ifilot/pico-sst39sf0x0-programmer/gui/tests/tst_mainwindow.cpp

#include <QtTest/QtTest>

#include "mainwindow.h"
#include "colorcontrast.h"
#include "support/emulated_serial_transport.h"
#include "support/fault_injecting_transport.h"

#include <QComboBox>
#include <QFile>
#include <QGroupBox>
#include <QLabel>
#include <QMessageBox>
#include <QProgressBar>
#include <QPushButton>
#include <QRegularExpression>
#include <QScrollArea>
#include <QScrollBar>
#include <QSet>
#include <QTimer>

#include <memory>

namespace {

class ModalDialogWatcher : public QObject {
public:
    QStringList messages;

    ModalDialogWatcher() {
        this->timer.setInterval(10);
        connect(&this->timer, &QTimer::timeout, this, &ModalDialogWatcher::captureAndAcceptDialogs);
        this->timer.start();
    }

    ~ModalDialogWatcher() override {
        this->timer.stop();
    }

private:
    QTimer timer;
    QSet<QWidget*> handled;

private:
    void captureAndAcceptDialogs() {
        const auto widgets = QApplication::topLevelWidgets();
        for(QWidget* widget : widgets) {
            if(this->handled.contains(widget)) {
                continue;
            }

            if(auto* box = qobject_cast<QMessageBox*>(widget)) {
                this->messages.append(box->text());
                this->handled.insert(widget);
                QTimer::singleShot(0, box, &QMessageBox::accept);
            }
        }
    }
};

}

class MainWindowTest : public QObject {
    Q_OBJECT

private:
    static MainWindow::SerialInterfaceFactory buildFactory(const std::shared_ptr<FirmwareEmulatorBackend>& backend) {
        return [backend](const std::string& portname) {
            return std::make_shared<SerialInterface>(portname, [backend](const std::string&) {
                return backend->create_transport();
            });
        };
    }

    static MainWindow::SerialInterfaceFactory buildFaultFactory(const std::shared_ptr<FirmwareEmulatorBackend>& backend,
                                                                const std::string& targetCommand,
                                                                FaultInjectingTransport::FaultMode mode) {
        return [backend, targetCommand, mode](const std::string& portname) {
            return std::make_shared<SerialInterface>(portname, [backend, targetCommand, mode](const std::string&) {
                return std::make_unique<FaultInjectingTransport>(
                    backend->create_transport(),
                    targetCommand,
                    mode
                );
            });
        };
    }

    static QComboBox* serialPortCombo(MainWindow& window) {
        return window.findChild<QComboBox*>("comboboxSerialPorts");
    }

    static QLabel* boardIdLabel(MainWindow& window) {
        return window.findChild<QLabel*>("labelBoardId");
    }

    static QLabel* serialLabel(MainWindow& window) {
        return window.findChild<QLabel*>("labelSerial");
    }

    static QLabel* chipTypeLabel(MainWindow& window) {
        return window.findChild<QLabel*>("labelChipType");
    }

    static QPushButton* button(MainWindow& window, const char* objectName) {
        return window.findChild<QPushButton*>(objectName);
    }

    static QProgressBar* progressBar(MainWindow& window) {
        return window.findChild<QProgressBar*>("progressBarLoad");
    }

    static HexViewWidget* hexView(MainWindow& window) {
        return window.findChild<HexViewWidget*>("hexViewWidget");
    }

    static void addEmulatedPort(MainWindow& window, const QString& portName = "emu") {
        auto* combo = serialPortCombo(window);
        QVERIFY(combo != nullptr);
        combo->addItem(portName);
        combo->setCurrentText(portName);
    }

private slots:
    void select_com_port_updates_labels_and_enables_buttons();
    void read_chip_id_updates_ui_state();
    void read_rom_populates_hex_view();
    void flash_rom_quick_runs_program_and_verify_workflow();
    void flash_rom_quick_worker_abort_is_reported();
    void destruction_waits_for_active_read();
    void menu_actions_have_visible_icons();
    void right_control_panel_fits_scroll_viewport();
    void hex_viewer_color_presets_and_swatches_are_accessible();
};

void MainWindowTest::hex_viewer_color_presets_and_swatches_are_accessible() {
    QCOMPARE(contrastingTextColor(QColor(Qt::white)), QColor(Qt::black));
    QCOMPARE(contrastingTextColor(QColor(Qt::black)), QColor(Qt::white));
    QCOMPARE(contrastingTextColor(QColor(QStringLiteral("#fdf6e3"))), QColor(Qt::black));
    QCOMPARE(contrastingTextColor(QColor(QStringLiteral("#282a36"))), QColor(Qt::white));

    SettingsWidget widget;
    auto* themes = widget.findChild<QComboBox*>("hexViewerThemeComboBox");
    QVERIFY(themes != nullptr);
    const QStringList accessibleThemes = {
        QStringLiteral("Dracula"),
        QStringLiteral("Dracula Alucard (Light)"),
        QStringLiteral("Nord"),
        QStringLiteral("Gruvbox Dark"),
        QStringLiteral("Catppuccin Mocha")
    };
    for(const QString& themeName : accessibleThemes) {
        const int index = themes->findText(themeName);
        QVERIFY2(index >= 0, qPrintable(themeName));
        const QVariantList colors = themes->itemData(index).toList();
        QCOMPARE(colors.size(), 6);
        const QColor background(colors.constFirst().toUInt());
        for(int i = 1; i < colors.size(); ++i) {
            const QColor foreground(colors.at(i).toUInt());
            QVERIFY2(colorContrastRatio(background, foreground) >= 4.5,
                     qPrintable(themeName + QStringLiteral(" color ") + foreground.name()));
        }
    }

    const int saa5050Index = themes->findText(QStringLiteral("SAA5050"));
    QVERIFY(saa5050Index >= 0);
    const QVariantList saa5050 = themes->itemData(saa5050Index).toList();
    QCOMPARE(saa5050.size(), 6);
    QCOMPARE(saa5050.at(3).toUInt(), 0xFFFFFFFFu);

    const auto swatches = widget.findChildren<QPushButton*>(
        QRegularExpression(QStringLiteral("^colorSwatch_")));
    QCOMPARE(swatches.size(), 6);
    for(QPushButton* swatch : swatches) {
        const QColor color = swatch->property("swatchColor").value<QColor>();
        QVERIFY(color.isValid());
        QCOMPARE(swatch->text(), color.name(QColor::HexRgb));
        QVERIFY(swatch->styleSheet().contains(contrastingTextColor(color).name()));
    }
}

void MainWindowTest::right_control_panel_fits_scroll_viewport() {
    auto logs = std::make_shared<QStringList>();
    MainWindow window(logs);
    window.resize(1000, 800);
    window.show();
    QApplication::processEvents();

    auto* scrollArea = window.findChild<QScrollArea*>("rightControlScrollArea");
    auto* controls = window.findChild<QWidget*>("rightControlContainer");
    QVERIFY(scrollArea != nullptr);
    QVERIFY(controls != nullptr);
    QCOMPARE(scrollArea->horizontalScrollBar()->maximum(), 0);
    QCOMPARE(controls->width(), scrollArea->viewport()->width());

    const QStringList groupNames = {
        QStringLiteral("serialInterfaceGroup"),
        QStringLiteral("romImagesGroup"),
        QStringLiteral("operationsGroup")
    };
    for(const QString& name : groupNames) {
        auto* group = controls->findChild<QGroupBox*>(name);
        QVERIFY2(group != nullptr, qPrintable(name));
        QVERIFY2(group->geometry().right() < controls->width(), qPrintable(name));
    }
}

void MainWindowTest::menu_actions_have_visible_icons() {
    auto logs = std::make_shared<QStringList>();
    MainWindow window(logs);

    const auto menuBarActions = window.menuBar()->actions();
    QCOMPARE(menuBarActions.size(), 3);
    for(QAction* menuBarAction : menuBarActions) {
        QMenu* menu = menuBarAction->menu();
        QVERIFY(menu != nullptr);
        for(QAction* action : menu->actions()) {
            QVERIFY2(!action->icon().isNull(), qPrintable(action->text()));
            QVERIFY2(action->isIconVisibleInMenu(), qPrintable(action->text()));
        }
    }

    QPushButton* romButton = nullptr;
    for(QPushButton* candidate : window.findChildren<QPushButton*>()) {
        if(candidate->text() == QStringLiteral("Select other ROM")) {
            romButton = candidate;
            break;
        }
    }

    QVERIFY(romButton != nullptr);
    QVERIFY(romButton->menu() != nullptr);
    QCOMPARE(romButton->menu()->actions().size(), 2);

    for(QAction* action : romButton->menu()->actions()) {
        QVERIFY2(!action->icon().isNull(), qPrintable(action->text()));
        QVERIFY2(action->isIconVisibleInMenu(), qPrintable(action->text()));
        QVERIFY2(action->menu() != nullptr, qPrintable(action->text()));
    }

    QMenu* p2000tMenu = romButton->menu()->actions().at(0)->menu();
    QMenu* p2000mMenu = romButton->menu()->actions().at(1)->menu();
    QCOMPARE(p2000tMenu->title(), QStringLiteral("Philips P2000T"));
    QCOMPARE(p2000mMenu->title(), QStringLiteral("Philips P2000M"));
    QCOMPARE(p2000tMenu->actions().size(), 14);
    QCOMPARE(p2000mMenu->actions().size(), 2);
    QVERIFY(p2000tMenu->menuAction()->icon().cacheKey()
            != p2000tMenu->actions().constFirst()->icon().cacheKey());
    QVERIFY(p2000mMenu->menuAction()->icon().cacheKey()
            != p2000mMenu->actions().constFirst()->icon().cacheKey());

    for(QAction* action : p2000tMenu->actions()) {
        QVERIFY2(!action->icon().isNull(), qPrintable(action->text()));
        QVERIFY2(action->isIconVisibleInMenu(), qPrintable(action->text()));
        QVERIFY2(action->property("image_name").isValid(), qPrintable(action->text()));
    }

    QCOMPARE(p2000mMenu->actions().at(0)->text(), QStringLiteral("MCPM"));
    QCOMPARE(p2000mMenu->actions().at(1)->text(), QStringLiteral("UCSD Pascal"));
    for(QAction* action : p2000mMenu->actions()) {
        QVERIFY2(!action->icon().isNull(), qPrintable(action->text()));
        QVERIFY2(action->isIconVisibleInMenu(), qPrintable(action->text()));

        QFile file(QStringLiteral(":/assets/roms/") + action->property("image_name").toString());
        QVERIFY2(file.open(QIODevice::ReadOnly), qPrintable(file.fileName()));
        QCOMPARE(file.size(), qint64(16 * 1024));

        const QByteArray data = file.readAll();
        if(action->text() == QStringLiteral("MCPM")) {
            QCOMPARE(data.right(8 * 1024), QByteArray(8 * 1024, static_cast<char>(0xFF)));
        }
    }
}

void MainWindowTest::select_com_port_updates_labels_and_enables_buttons() {
    auto backend = std::make_shared<FirmwareEmulatorBackend>();
    auto logs = std::make_shared<QStringList>();
    MainWindow window(logs, nullptr, buildFactory(backend));

    addEmulatedPort(window);

    QVERIFY(QMetaObject::invokeMethod(&window, "select_com_port", Qt::DirectConnection));

    QCOMPARE(serialLabel(window)->text(), QString("Port: emu"));
    QVERIFY(boardIdLabel(window)->text().contains("PICOSST39-V1.3.0"));
    QVERIFY(button(window, "buttonIdentifyChip")->isEnabled());
    QVERIFY(button(window, "buttonReadCartridge")->isEnabled());
}

void MainWindowTest::read_chip_id_updates_ui_state() {
    auto backend = std::make_shared<FirmwareEmulatorBackend>(QByteArray(), QByteArray("PICOSST39-V1.3.0"), 0xBFB6);
    auto logs = std::make_shared<QStringList>();
    MainWindow window(logs, nullptr, buildFactory(backend));

    addEmulatedPort(window);
    QVERIFY(QMetaObject::invokeMethod(&window, "select_com_port", Qt::DirectConnection));
    QVERIFY(QMetaObject::invokeMethod(&window, "read_chip_id", Qt::DirectConnection));

    QCOMPARE(chipTypeLabel(window)->text(), QString("ROM chip: SST39SF020"));
    QCOMPARE(progressBar(window)->maximum(), 256 * 1024 / 256);
    QVERIFY(button(window, "buttonReadRom")->isEnabled());
    QVERIFY(button(window, "buttonFlashRom")->isEnabled());
    QVERIFY(button(window, "buttonFlashBank")->isEnabled());
    QVERIFY(button(window, "buttonEraseChip")->isEnabled());
    QVERIFY(button(window, "buttonScanSlots")->isEnabled());
}

void MainWindowTest::read_rom_populates_hex_view() {
    QByteArray flash(128 * 1024, static_cast<char>(0xFF));
    for(int i=0; i<flash.size(); i++) {
        flash[i] = static_cast<char>(i & 0xFF);
    }

    auto backend = std::make_shared<FirmwareEmulatorBackend>(flash, QByteArray("PICOSST39-V1.3.0"), 0xBFB5);
    auto logs = std::make_shared<QStringList>();
    MainWindow window(logs, nullptr, buildFactory(backend));

    addEmulatedPort(window);
    QVERIFY(QMetaObject::invokeMethod(&window, "select_com_port", Qt::DirectConnection));
    QVERIFY(QMetaObject::invokeMethod(&window, "read_chip_id", Qt::DirectConnection));
    QVERIFY(QMetaObject::invokeMethod(&window, "read_rom", Qt::DirectConnection));

    QTRY_COMPARE(hexView(window)->get_data().size(), flash.size());
    QCOMPARE(hexView(window)->get_data().left(256), flash.left(256));
    QVERIFY(window.statusBar()->currentMessage().contains("Done reading chip"));
}

void MainWindowTest::flash_rom_quick_runs_program_and_verify_workflow() {
    auto backend = std::make_shared<FirmwareEmulatorBackend>(QByteArray(), QByteArray("PICOSST39-V1.3.0"), 0xBFB5);
    auto logs = std::make_shared<QStringList>();
    MainWindow window(logs, nullptr, buildFactory(backend));
    ModalDialogWatcher watcher;

    addEmulatedPort(window);
    QVERIFY(QMetaObject::invokeMethod(&window, "select_com_port", Qt::DirectConnection));
    QVERIFY(QMetaObject::invokeMethod(&window, "read_chip_id", Qt::DirectConnection));

    QByteArray bankData(0x4000, static_cast<char>(0xFF));
    for(int i=0; i<bankData.size(); i++) {
        bankData[i] = static_cast<char>((i * 9) & 0xFF);
    }
    hexView(window)->set_data(bankData);

    QVERIFY(QMetaObject::invokeMethod(&window, "flash_rom_quick", Qt::DirectConnection));

    QTRY_VERIFY(watcher.messages.join("\n").contains("Cartridge was successfully flashed"));
    QCOMPARE(backend->flashContents().mid(0, bankData.size()), bankData);
    QTRY_VERIFY(progressBar(window)->value() <= 0);
}

void MainWindowTest::flash_rom_quick_worker_abort_is_reported() {
    auto backend = std::make_shared<FirmwareEmulatorBackend>(QByteArray(), QByteArray("PICOSST39-V1.3.0"), 0xBFB5);
    auto logs = std::make_shared<QStringList>();
    MainWindow window(logs, nullptr, buildFaultFactory(backend, "WRSECT00", FaultInjectingTransport::FaultMode::CorruptEcho));
    ModalDialogWatcher watcher;

    addEmulatedPort(window);
    QVERIFY(QMetaObject::invokeMethod(&window, "select_com_port", Qt::DirectConnection));
    QVERIFY(QMetaObject::invokeMethod(&window, "read_chip_id", Qt::DirectConnection));

    QByteArray bankData(0x4000, static_cast<char>(0xAA));
    hexView(window)->set_data(bankData);

    QVERIFY(QMetaObject::invokeMethod(&window, "flash_rom_quick", Qt::DirectConnection));

    QTRY_VERIFY(watcher.messages.join("\n").contains("Operation terminated unexpectedly"));
}

void MainWindowTest::destruction_waits_for_active_read() {
    auto backend = std::make_shared<FirmwareEmulatorBackend>(
        QByteArray(128 * 1024, static_cast<char>(0xA5)),
        QByteArray("PICOSST39-V1.3.0"),
        0xBFB5
    );

    {
        auto logs = std::make_shared<QStringList>();
        MainWindow window(logs, nullptr, buildFactory(backend));

        addEmulatedPort(window);
        QVERIFY(QMetaObject::invokeMethod(&window, "select_com_port", Qt::DirectConnection));
        QVERIFY(QMetaObject::invokeMethod(&window, "read_chip_id", Qt::DirectConnection));
        QVERIFY(QMetaObject::invokeMethod(&window, "read_rom", Qt::DirectConnection));
    }

    const auto history = backend->commandHistory();
    QCOMPARE(QString::fromStdString(history.back()), QString("RDBANK07"));
}

QTEST_MAIN(MainWindowTest)

#include "tst_mainwindow.moc"
