ifilot/pico-sst39sf0x0-programmer/gui/src/readthread.h

/****************************************************************************
 *                                                                          *
 *   PICO-SST39SF0x0-FLASHER                                                *
 *   Copyright (C) 2023 Ivo Filot <ivo@ivofilot.nl>                         *
 *                                                                          *
 *   This program is free software: you can redistribute it and/or modify   *
 *   it under the terms of the GNU Lesser General Public License as         *
 *   published by the Free Software Foundation, either version 3 of the     *
 *   License, or (at your option) any later version.                        *
 *                                                                          *
 *   This program is distributed in the hope that it will be useful,        *
 *   but WITHOUT ANY WARRANTY; without even the implied warranty of         *
 *   MERCHANTABILITY or FITNESS FOR A PARTICULAR PURPOSE.  See the          *
 *   GNU General Public License for more details.                           *
 *                                                                          *
 *   You should have received a copy of the GNU General Public license      *
 *   along with this program.  If not, see <https://www.gnu.org/licenses/>. *
 *                                                                          *
 ****************************************************************************/

#ifndef READTHREAD_H
#define READTHREAD_H

#include <iostream>
#include <QDebug>

#include "ioworker.h"
#include "romsizes.h"

/**
 * @brief Worker Thread responsible for reading ROM from cartridge
 */
class ReadThread : public IOWorker {

    Q_OBJECT

private:
    uint8_t nr_banks = 0;       // number of banks to read
    uint8_t starting_bank = 0;      // bank to start reading from

public:
    /**
     * @brief Default constructor.
     */
    ReadThread() {}

    /**
     * @brief Construct a reader thread.
     * @param _serial_interface shared serial interface
     * @param _starting_bank bank to start reading from
     * @param _nr_banks number of banks to read, or zero to auto-detect
     */
    ReadThread(const std::shared_ptr<SerialInterface>& _serial_interface,
               uint8_t _starting_bank = 0,
               uint8_t _nr_banks = 0) :
        IOWorker(_serial_interface),
        nr_banks(_nr_banks),
        starting_bank(_starting_bank) {}

    /**
     * @brief read the ROM from a cartridge
     *
     * This routine will be called when a thread containing this
     * class is runned
     */
    void run() override;

    /**
     * @brief set the number of roms banks
     * @param number of rom banks
     */
    inline void set_number_rom_banks(unsigned int _nr_banks) {
        this->nr_banks = _nr_banks;
    }

signals:
    /**
     * @brief signal when rom has been read
     */
    void read_result_ready();

    /**
     * @brief signal when a new block is about to be read
     * @param sector_id
     */
    void read_block_start(unsigned int block_id, unsigned int nr_blocks);

    /**
     * @brief signal when a new block is read
     * @param sector_id
     */
    void read_block_done(unsigned int block_id, unsigned int nr_blocks);
};

#endif // READTHREAD_H
